misaacastillo/RoboticArm/mechanical/Piezas 3D/Cuerpo21.stl

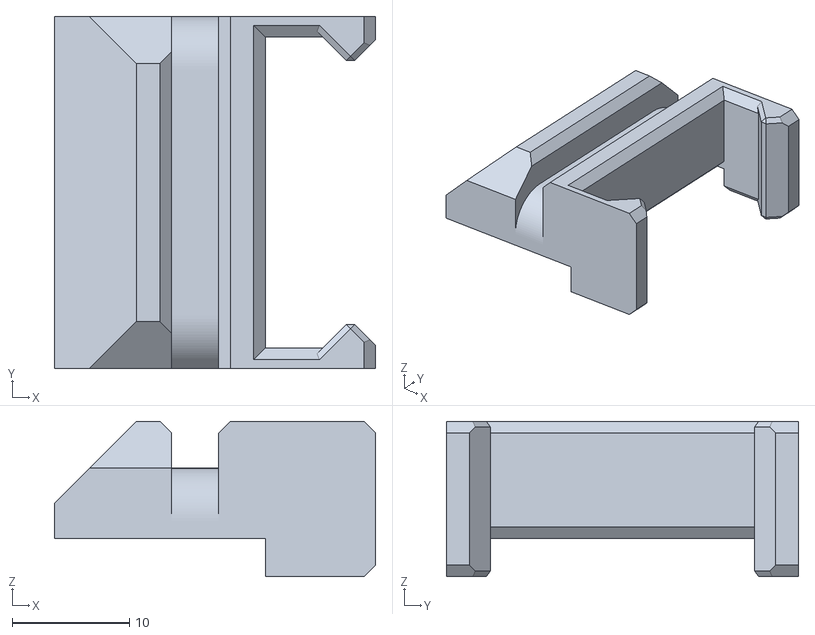
[picture p20: CAD file, 2024-11-27]
mechanical/Piezas 3D/Cuerpo21.stl
27.4 x 30.0 x 13.2
