misaacastillo/RoboticArm/mechanical/Piezas 3D/Cuerpo18.stl

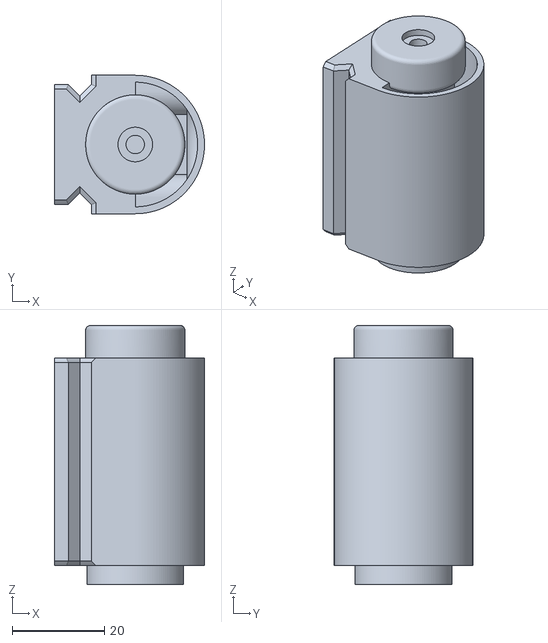
[picture p21: CAD file, 2024-11-27]
mechanical/Piezas 3D/Cuerpo18.stl
32.5 x 30.0 x 56.1
