misaacastillo/RoboticArm/mechanical/Piezas 3D/tapa inferior.3mf

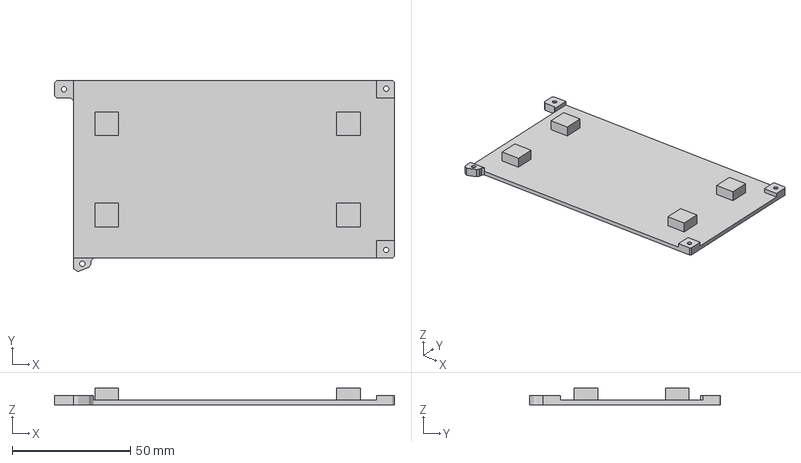
[picture p22: CAD file, 2024-11-27]
mechanical/Piezas 3D/tapa inferior.3mf
143.5 x 80.7 x 7.00 mm
