misaacastillo/RoboticArm/mechanical/Piezas 3D/Cuerpo11.stl

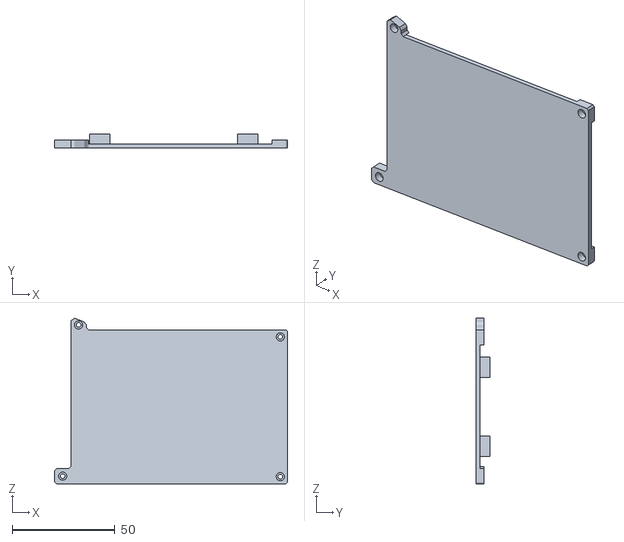
[picture p23: CAD file, 2024-11-27]
mechanical/Piezas 3D/Cuerpo11.stl
113.5 x 7.00 x 80.7
