misaacastillo/RoboticArm/mechanical/Piezas 3D/Robotic Arm Proyect.3mf

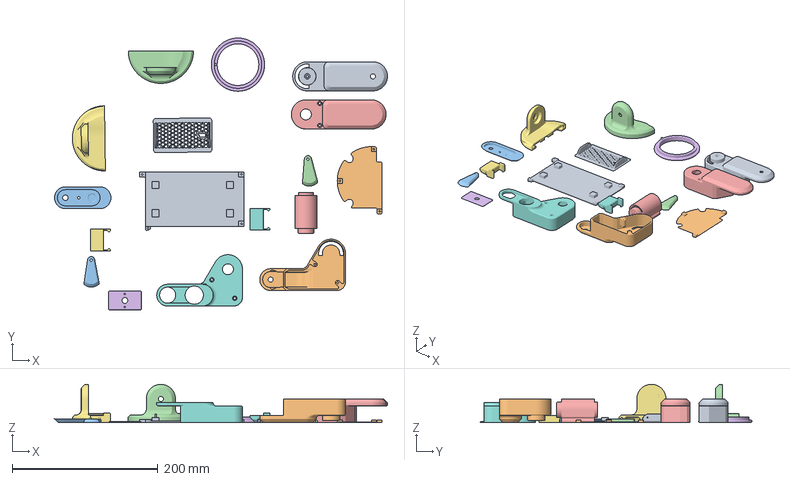
[picture p24: CAD file, 2024-11-27]
mechanical/Piezas 3D/Robotic Arm Proyect.3mf
456.6 x 372.9 x 52.5 mm
Cuerpo1.stl
Cuerpo2.stl
Cuerpo3.stl
Cuerpo5.stl
Cuerpo4.stl
Cuerpo6.stl
Cuerpo7.stl
Cuerpo8.stl
Cuerpo9.stl
Cuerpo12.stl
Cuerpo15.stl
Cuerpo16.stl
Cuerpo18.stl
Cuerpo19.stl
Cuerpo20.stl
Cuerpo21.stl
tapa inferior
