misaacastillo/RoboticArm/mechanical/Piezas 3D/Cuerpo19.stl

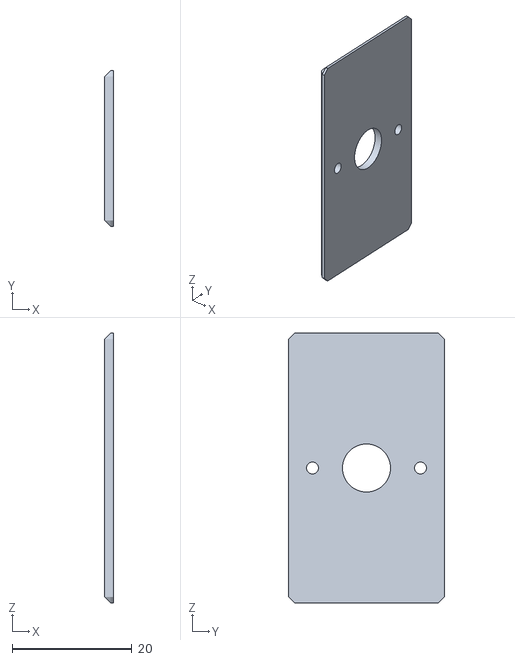
[picture p25: CAD file, 2024-11-27]
mechanical/Piezas 3D/Cuerpo19.stl
1.50 x 26.0 x 45.0
