misaacastillo/RoboticArm/mechanical/Piezas 3D/Cuerpo9.stl

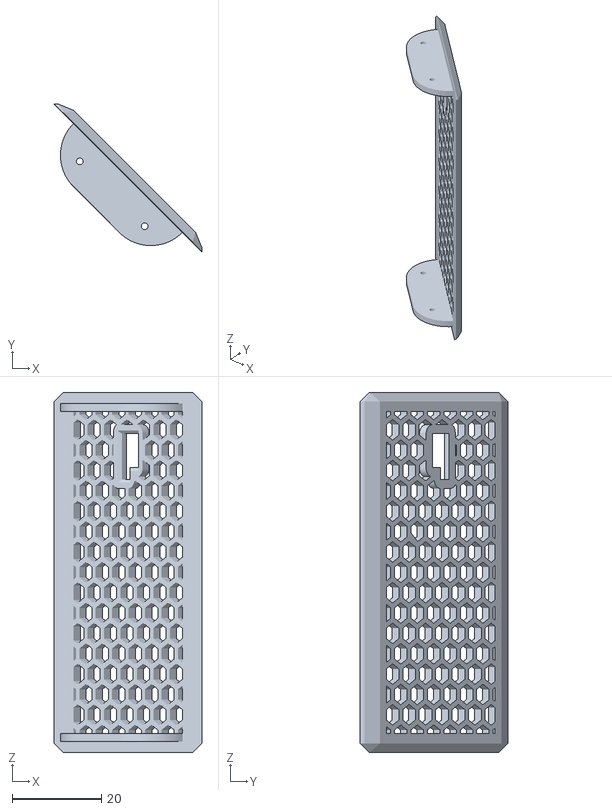
[picture p26: CAD file, 2024-11-27]
mechanical/Piezas 3D/Cuerpo9.stl
33.0 x 33.0 x 80.5
