misaacastillo/RoboticArm/mechanical/Piezas 3D/Cuerpo4 AR-4.3mf

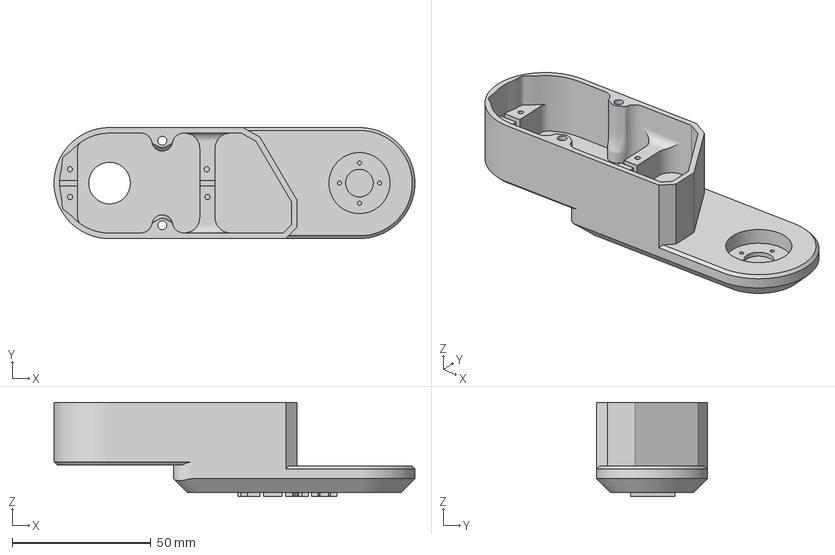
[picture p27: CAD file, 2024-11-27]
mechanical/Piezas 3D/Cuerpo4 AR-4.3mf
130.0 x 39.9 x 34.0 mm
